RobThree/TemperatureDisplay/img/PCBWay/1.jpg

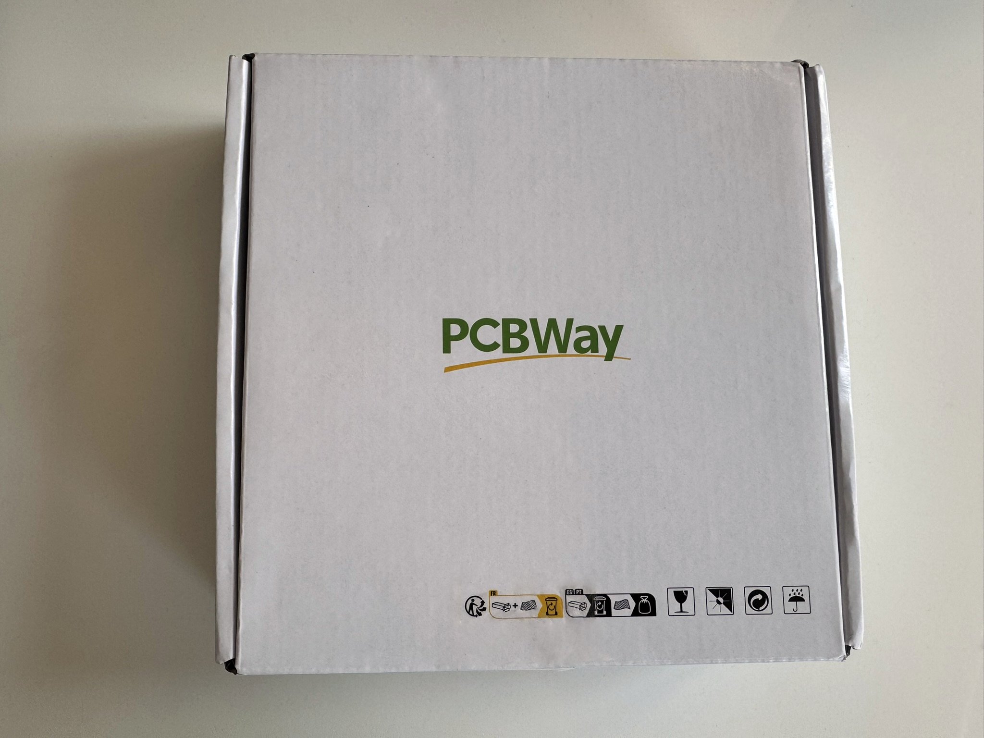
img/PCBWay/1.jpg
