RobThree/TemperatureDisplay/img/PCBWay/2.jpg

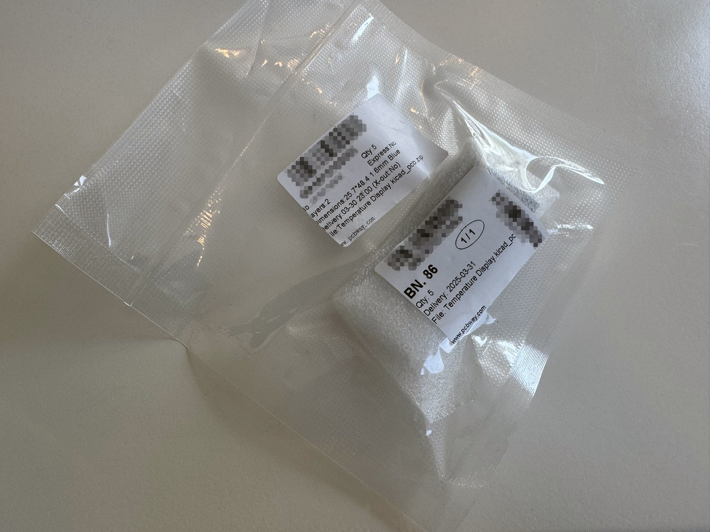
img/PCBWay/2.jpg
