RobThree/TemperatureDisplay/img/PCBWay/3.jpg

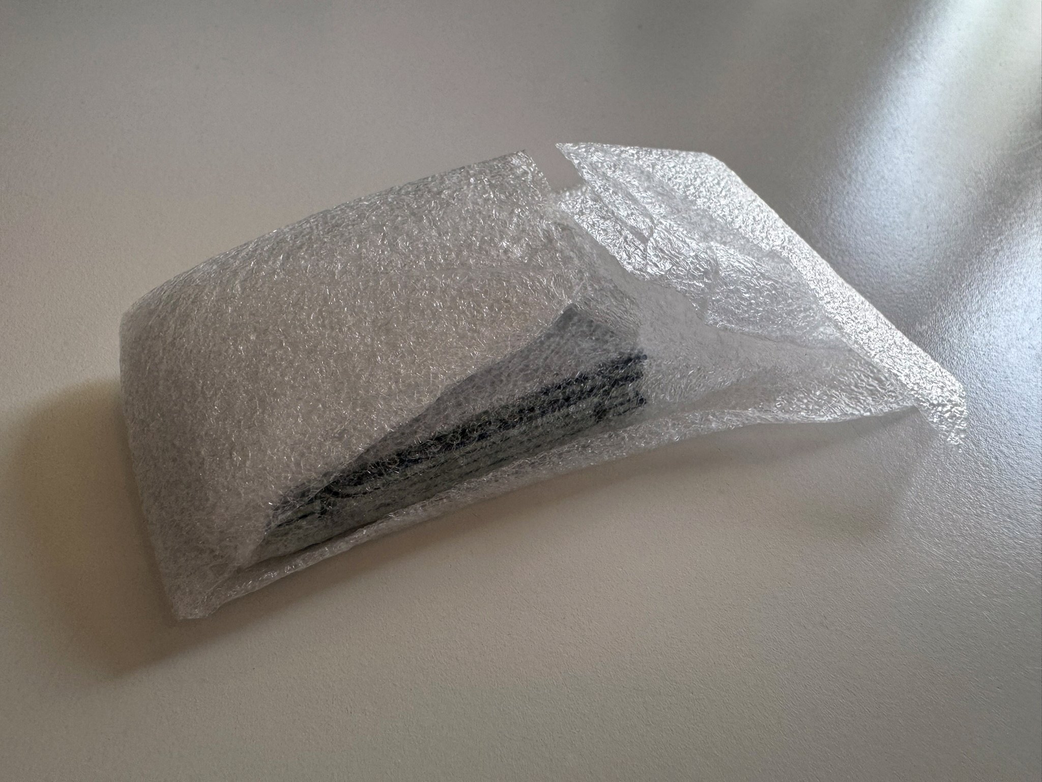
img/PCBWay/3.jpg
