RobThree/TemperatureDisplay/img/PCBWay/4.jpg

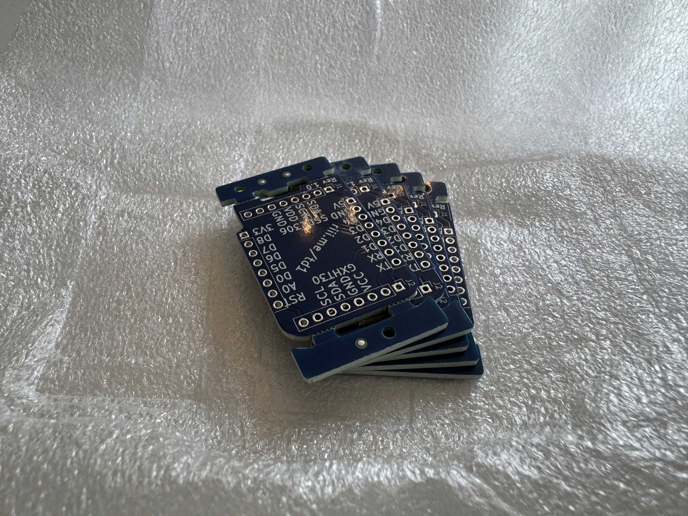
img/PCBWay/4.jpg
