RobThree/TemperatureDisplay/img/PCBWay/5.jpg

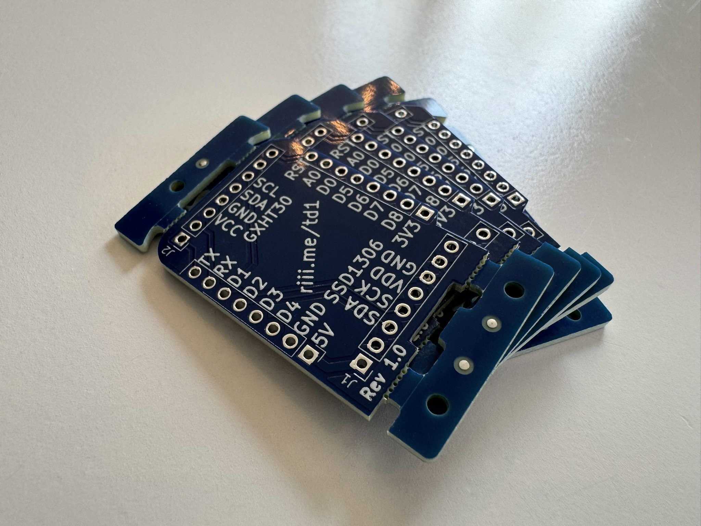
img/PCBWay/5.jpg
