RobThree/TemperatureDisplay/img/PCBWay/9.jpg

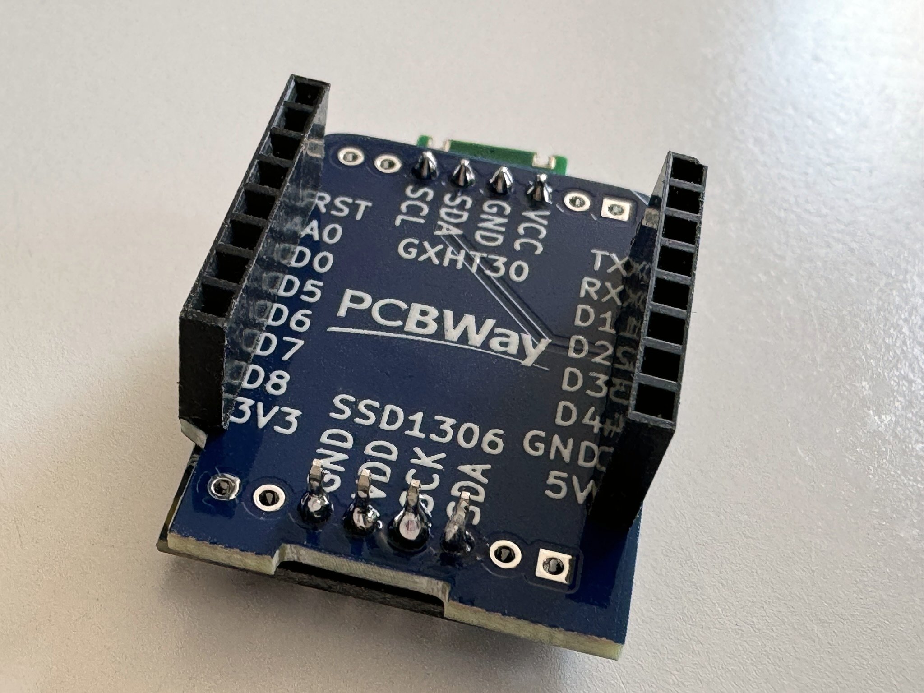
img/PCBWay/9.jpg
