RobThree/TemperatureDisplay/img/PCBWay/10.jpg

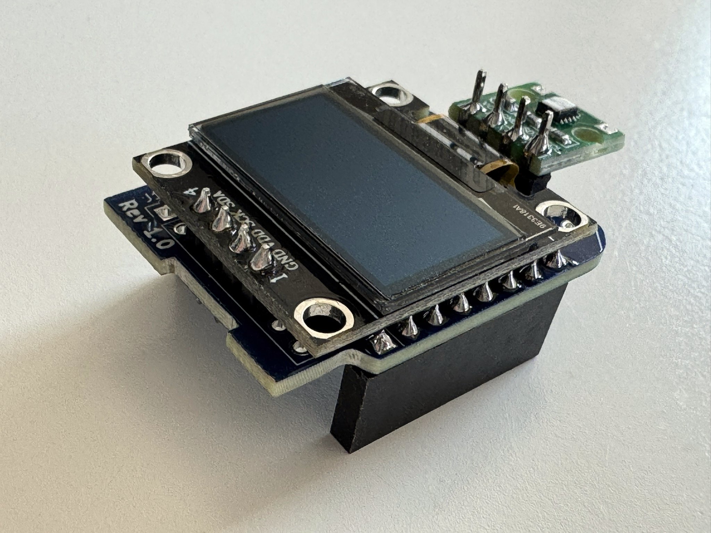
img/PCBWay/10.jpg
