RobThree/TemperatureDisplay/img/PCBWay/11.jpg

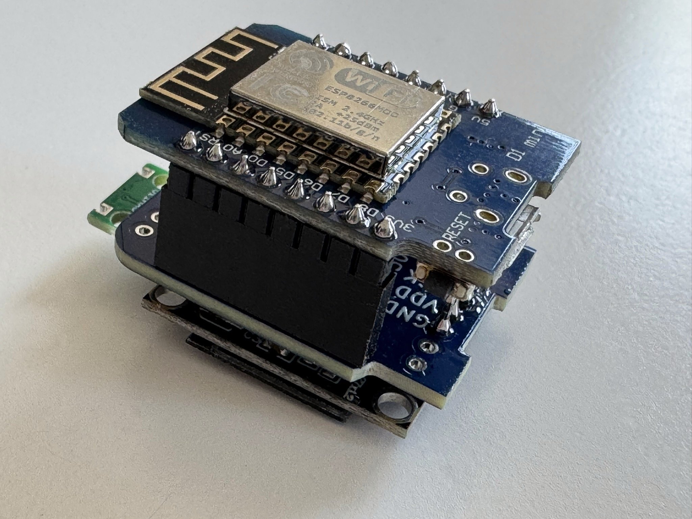
img/PCBWay/11.jpg
