RobThree/TemperatureDisplay/img/PCBWay/12.jpg

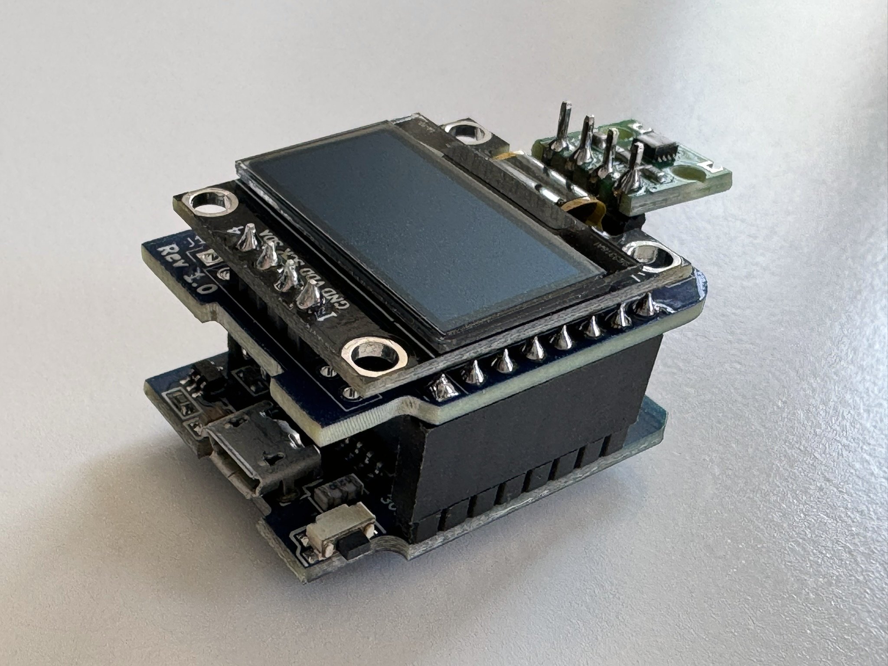
img/PCBWay/12.jpg
