RobThree/TemperatureDisplay/img/PCBWay/13.jpg

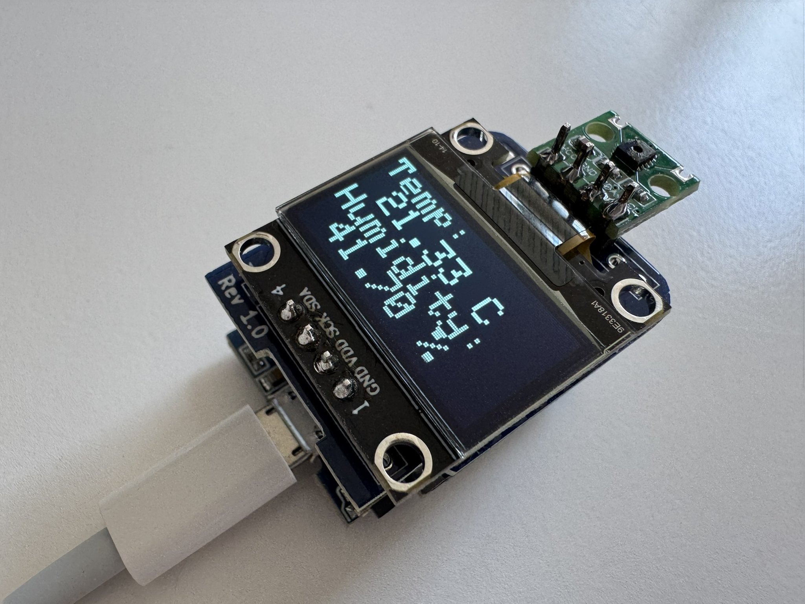
img/PCBWay/13.jpg
