RobThree/TemperatureDisplay/img/spacer.jpg

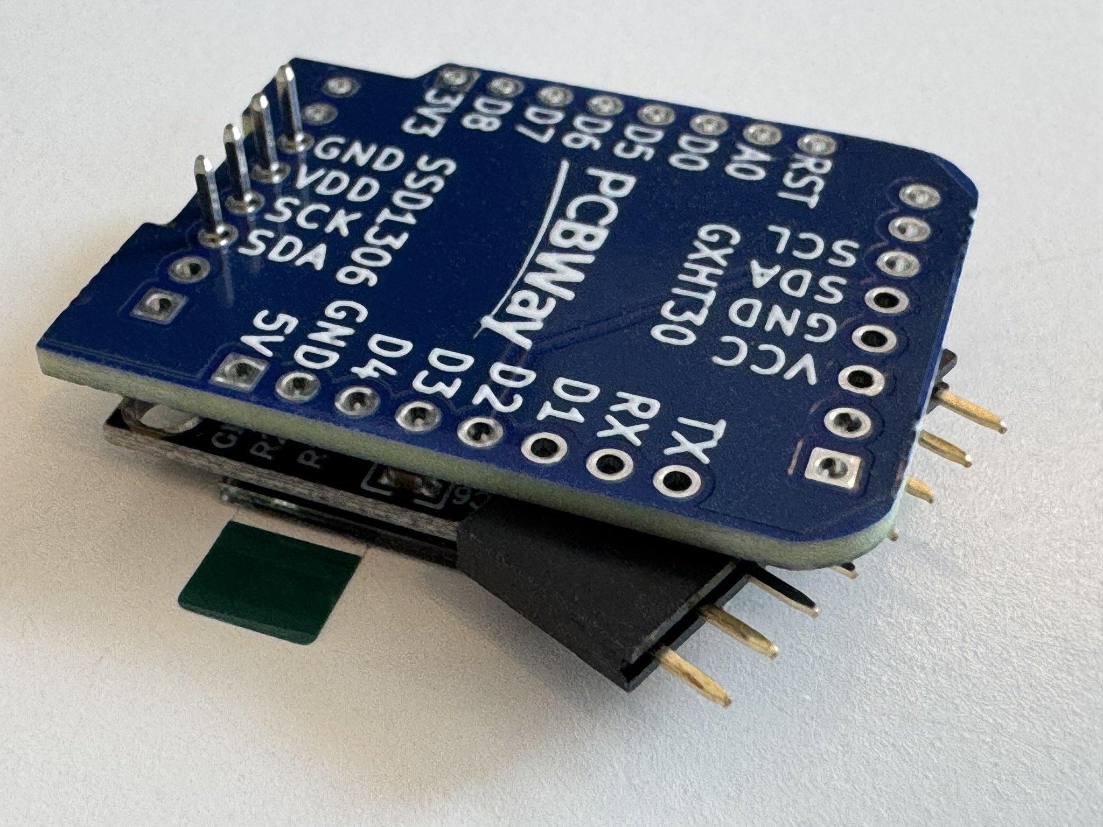
img/spacer.jpg
